rafinjahan/Object_Detection_Using_A_Smart_Pressure_Sensing_Textile_Mat/images/confusion_matrix_grouped_cv.png

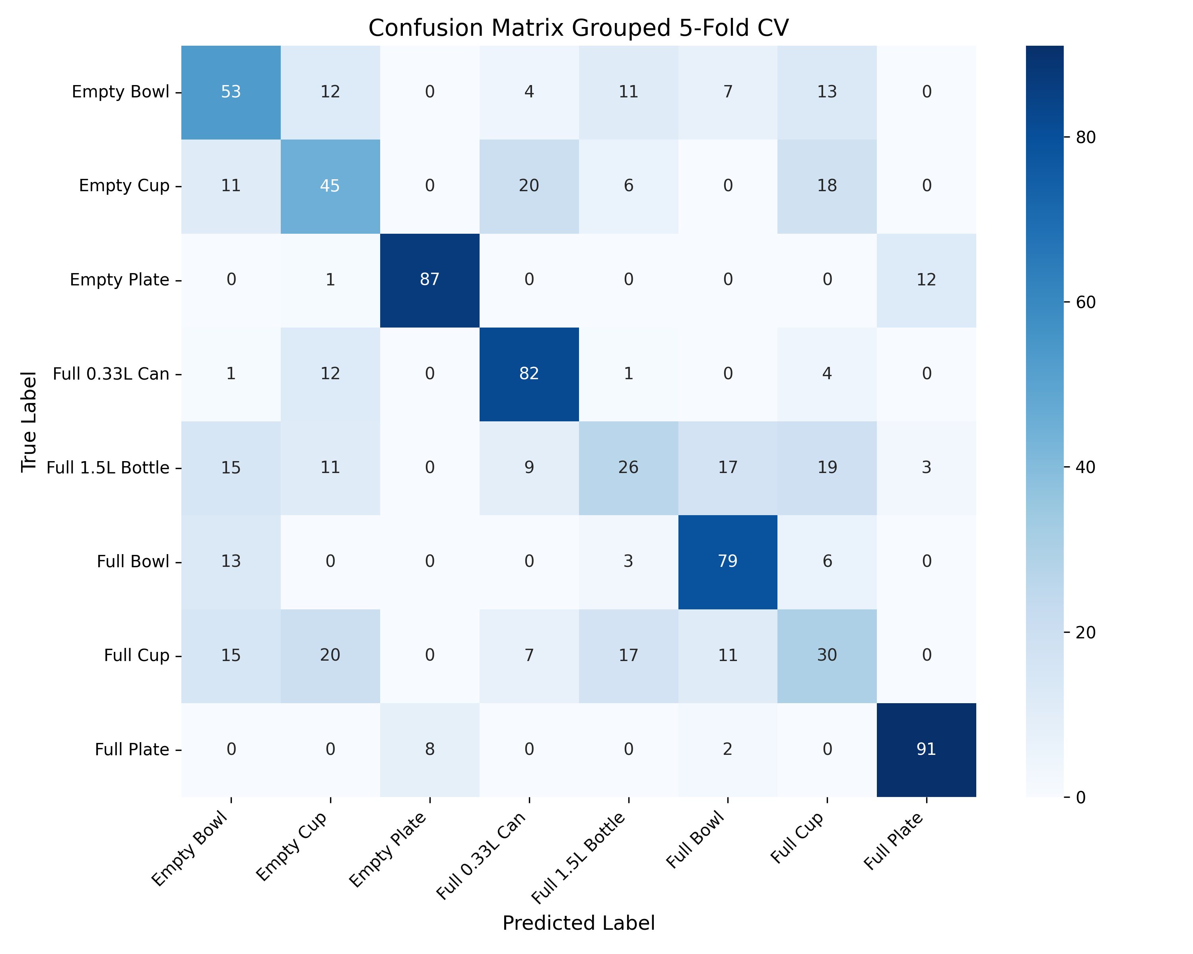
images/confusion_matrix_grouped_cv.png
