rafinjahan/Object_Detection_Using_A_Smart_Pressure_Sensing_Textile_Mat/images/sensitivity_deltaR_plot.png

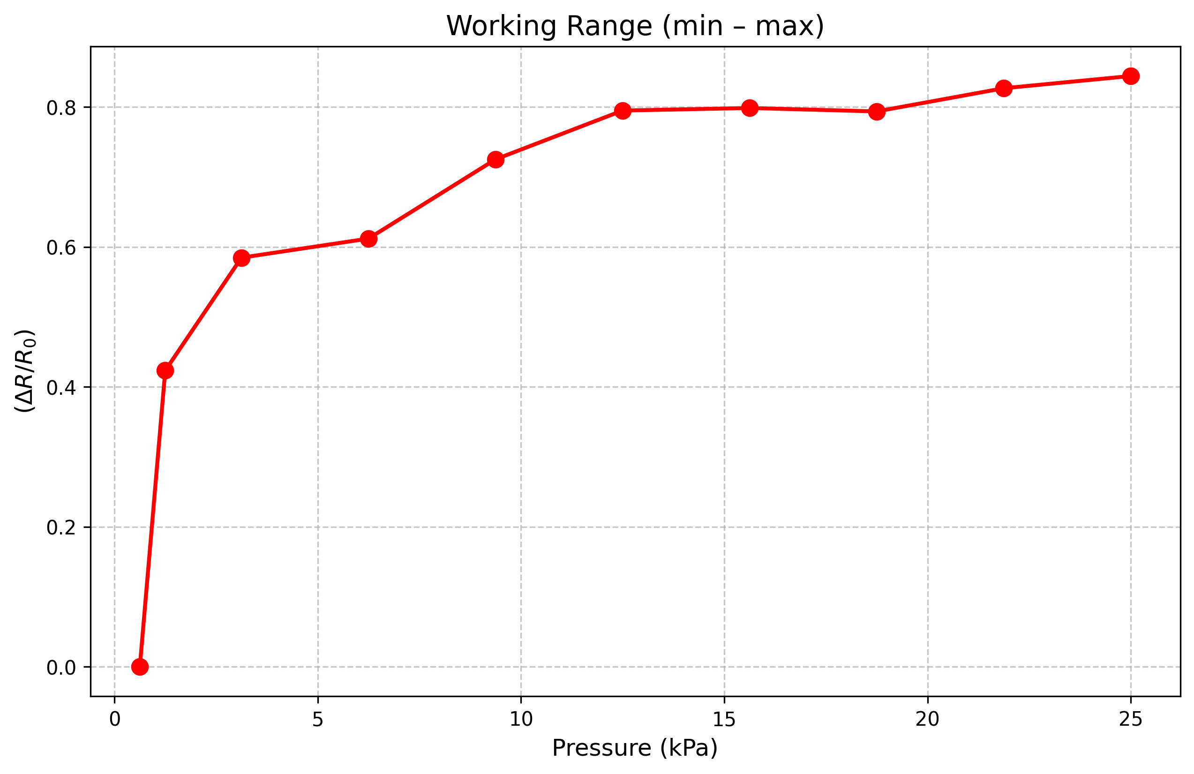
images/sensitivity_deltaR_plot.png
