rafinjahan/Object_Detection_Using_A_Smart_Pressure_Sensing_Textile_Mat/images/staircase_plot_puhdistettu.png

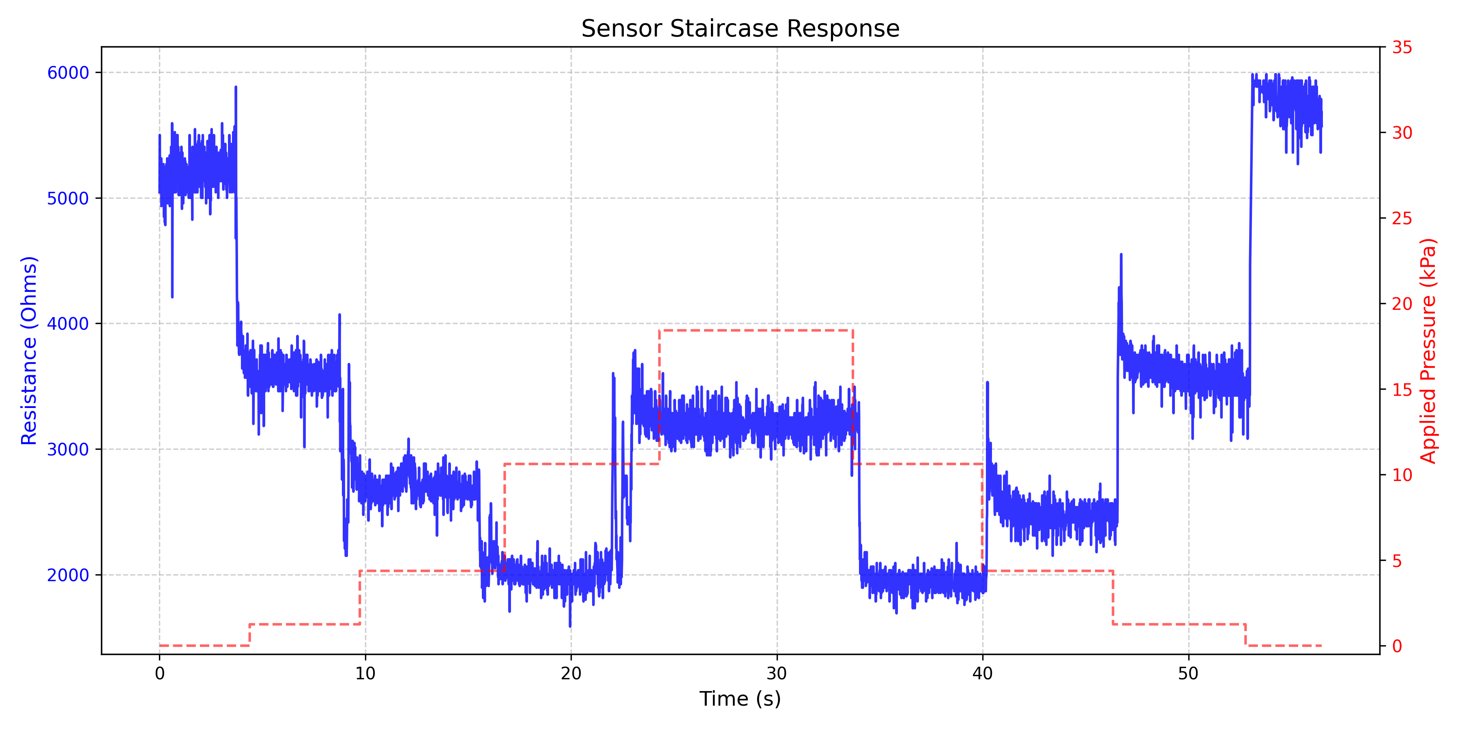
images/staircase_plot_puhdistettu.png
