rafinjahan/Object_Detection_Using_A_Smart_Pressure_Sensing_Textile_Mat/code/plot.py

import pandas as pd
import matplotlib.pyplot as plt
import os

script_folder = os.path.dirname(os.path.abspath(__file__))
project_root = os.path.dirname(script_folder)
data_folder = os.path.join(project_root, 'data')
images_folder = os.path.join(project_root, 'images')

df_sens = pd.read_csv(os.path.join(data_folder, 'sensitivity_range32.csv'), sep=';')
df_sens = df_sens[df_sens['weight_grams'] < 1000]

means = df_sens.groupby('weight_grams')['avg_resistance_ohms'].mean().reset_index()
means['pressure_kpa'] = means['weight_grams'] * 0.03124

df_resp = pd.read_csv(os.path.join(data_folder, 'response_time_400g.csv'), sep=';')
df_resp['time_ms'] = (df_resp['timestamp'] - df_resp['timestamp'].iloc[0]) * 1000

df_rec = pd.read_csv(os.path.join(data_folder, 'recovery_time_400g.csv'), sep=';')
df_rec['time_ms'] = (df_rec['timestamp'] - df_rec['timestamp'].iloc[0]) * 1000


plt.figure(figsize=(10, 6))
plt.plot(means['pressure_kpa'], means['avg_resistance_ohms'], 'b-o', linewidth=2)
plt.title('Sensor Sensitivity: Resistance vs Pressure', fontsize=14)
plt.xlabel('Pressure (kPa)', fontsize=12)
plt.ylabel('Resistance (Ohms)', fontsize=12)
plt.grid(True, linestyle='--', alpha=0.7)
plt.savefig(os.path.join(images_folder, 'sensitivity_plot.png'), dpi=300)


plt.figure(figsize=(10, 6))
plt.plot(df_resp['time_ms'], df_resp['resistance_ohms'], 'r-', linewidth=1.5)
plt.title('Response Time: High-Speed Loading (400g)', fontsize=14)
plt.xlabel('Time (ms)', fontsize=12)
plt.ylabel('Resistance (Ohms)', fontsize=12)
plt.grid(True, linestyle='--', alpha=0.7)
plt.savefig(os.path.join(images_folder, 'response_plot.png'), dpi=300)

plt.figure(figsize=(10, 6))
plt.plot(df_rec['time_ms'], df_rec['resistance_ohms'], 'g-', linewidth=1.5)
plt.title('Recovery Time: High-Speed Unloading (400g)', fontsize=14)
plt.xlabel('Time (ms)', fontsize=12)
plt.ylabel('Resistance (Ohms)', fontsize=12)
plt.grid(True, linestyle='--', alpha=0.7)
plt.savefig(os.path.join(images_folder, 'recovery_plot.png'), dpi=300)

print("Kaikki kuvaajat generoitu ja tallennettu kansioon.")
